ShubUtum/micromouse-2019/uart.c

/*
 * File:   uart.c
 * Author: gaoyingqiang
 *
 * Created on November 19, 2019, 10:44 AM
 */

#include <string.h> //for strlen()
#include "xc.h"
#include "uart.h"
#include <ctype.h>
#include "timer.h"
#include "gpio.h"
#include <stdlib.h> // for atoi()
#include "pwm.h"
#include "fsm.h"

static void uart2_interrupt_init( void );
static void set_receive_priority( void );

char log_str[MAX_LOG_STR_LEN];

uint16_t configUART2( float baud_rate, uint16_t fcy) //baud_rate in k, fcy in M
{
   unsigned int i;
    float baud_rate_U2BRG;
    baud_rate_U2BRG = (fcy * 1000000 / (16 * (baud_rate * 1000)) ) - 1;
    baud_rate_U2BRG = (int) baud_rate_U2BRG;
   // baud_rate_U2BRG = 16;
    U2MODEbits.UARTEN    = 0;     // disable UART
    U2BRG                = baud_rate_U2BRG;    // set baud rate to 57.6k bit/s
    U2MODEbits.LPBACK    = 0;     //disable loop-back mode
    U2MODEbits.WAKE      = 0;     // disable wake-up
    U2MODEbits.ABAUD     = 0;     // disable baud rate measurement 
    U2MODEbits.PDSEL     = 0b00;  // 8 bit data, no parity
    U2MODEbits.STSEL     = 0;     // one stop bit
    U2STAbits.URXISEL    = 0b00;  // interrupt when 1 character arrived
    IFS1bits.U2RXIF      = 0; // clear interrupt request flag
    IPC7bits.U2RXIP      = 0b100; // interrupt priority 4
    IEC1bits.U2RXIE      = 1;  // receive interrupt request enabled
    U2MODEbits.UARTEN    = 1;     // enable UART
    U2STAbits.UTXEN      = 1;     // enable transmit
    
    IEC1bits.U2TXIE = 0; // transmit interrupt interrupt request enabled
    
    uart2_interrupt_init();
    set_receive_priority(); 

    for (i = 0; i < 40000; i++); // short delay ~ 1ms

    return 0;
}

static void uart2_interrupt_init( void ) {
    IEC1bits.U2RXIE = 1;  // receive interrupt request not enabled
    IFS1bits.U2RXIF = 0; // receive interrupt request has occurred
    IEC1bits.U2TXIE = 0; // transmit interrupt interrupt request enabled
}

static void set_receive_priority( void) {
    IFS1bits.U2RXIF=1; // interrupt request occured
}

void send_A2Z( void )
{
    static uint16_t char_A2Z = 'A';
    U2TXREG = char_A2Z;
    char_A2Z ++;
    if(char_A2Z > 'Z')
    {
        char_A2Z = 'A';
    }
}

void send_char( char c ) // send one byte at a time
{    
    while(U2STAbits.UTXBF == 1); //wait until buffer is not full
    U2TXREG = c;   
}

void mySendString( char* stringinp )
{    
    while(*stringinp != '\0'){
        send_char(*stringinp);
        stringinp++;
    }   
}
 
void adjust_LED4( void )
{ 
    char char_dc[5];
    int counter = 0;
    while(IFS1bits.U2RXIF==1) // receive interrupt triggered
    {
        if(U2RXREG != '<' && U2RXREG != '>') // copy the contents between <>
        {
            char_dc[counter] = U2RXREG;
            counter = counter + 1;
            IFS1bits.U2RXIF = 0;
        } 
    }
    
    int i = 0;
    int j = 0;
    char rplstr[10] = "OK:";
    int invalid_fc = 0;
    while(i<strlen(char_dc))
    {
        if(~isdigit(char_dc[i])) // if char_dc contains non-numbers
        {
            mySendString("ERROR!");
            i = i + 1;
            invalid_fc = 1;
            break;
        }
        else
        {
            rplstr[2+j] = char_dc[i];
            j = j+ 1;
        }
    }
    
    if(~invalid_fc)
    {
        char *reply = rplstr;
        mySendString(reply);
    }
   
    int int_dc = atoi(char_dc);
    if(int_dc > 0 && int_dc <= 100)
    {
        pwm2_change_dc( int_dc );
    }
    else
    {
        mySendString("ERROR!");
    }
}

void __attribute__((interrupt, no_auto_psv)) _U2RXInterrupt(void)
{
    char myReceive;
    
    IFS1bits.U2RXIF = 0;     // clear Rx interrupt flag
    GREEN_LED = ~GREEN_LED; // toggle GREEN_LED when Rx Interrupt is called
    
    if(U2STAbits.OERR==1) // if Receive buffer has overflowed
    {
        U2STAbits.OERR = 0;
    }
    myReceive = U2RXREG;
    //send_char(myReceive);
    if( myReceive == '1' )       fsm_handle_event(SINGLE_CLICK_EVENT);
    else if( myReceive == '2' )  fsm_handle_event(DOUBLE_CLICK_EVENT);
    else if( myReceive == '3' )  fsm_handle_event(LONG_CLICK_EVENT);
    U2RXREG = '\0';
}

void __attribute__((interrupt, no_auto_psv)) _U2TXInterrupt(void)
{
    while(U2STAbits.TRMT == 0) // Transmit Shift register is not empty
    {
        IFS1bits.U2TXIF = 0;     // clear Tx interrupt flag 
    }
}
