ShubUtum/micromouse-2019/pushButton.h

/* 
 * File:   pushButton.h
 * Author: Khaled
 *
 * Created on February 16, 2020, 9:14 PM
 */

#ifndef PUSHBUTTON_H
#define	PUSHBUTTON_H


void check_push_button( uint16_t time_tick );

#endif	/* PUSHBUTTON_H */
